neuman/gripster/references/8bitdos-official-new-xbox-mobile-controller-includes-hall-effect-sticks-and-triggers-4.large.webp

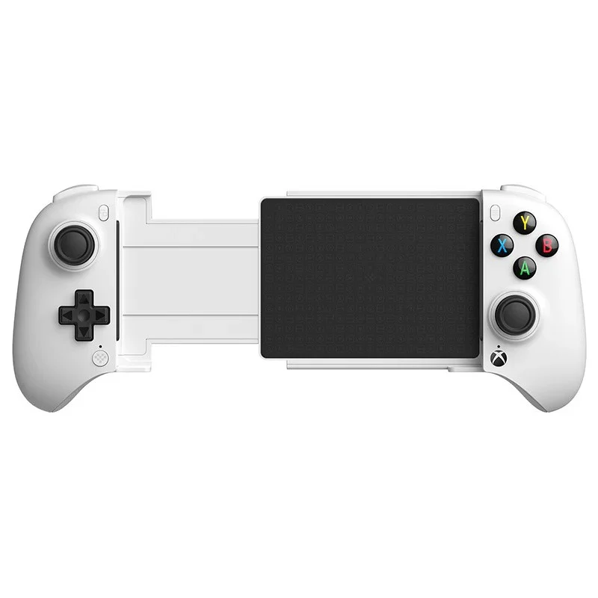
references/8bitdos-official-new-xbox-mobile-controller-includes-hall-effect-sticks-and-triggers-4.large.webp
