neuman/gripster/references/61UZpFPT2iS._AC_UF1000,1000_QL80_.jpg

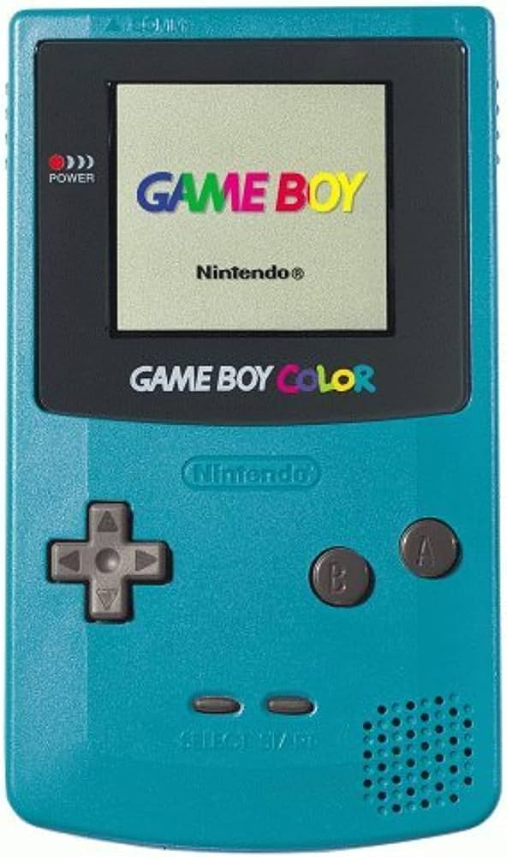
references/61UZpFPT2iS._AC_UF1000,1000_QL80_.jpg
