neuman/gripster/references/13225-tay-cam-choi-game-razer-kishi-v3-phantom-white-edition-5.jpg

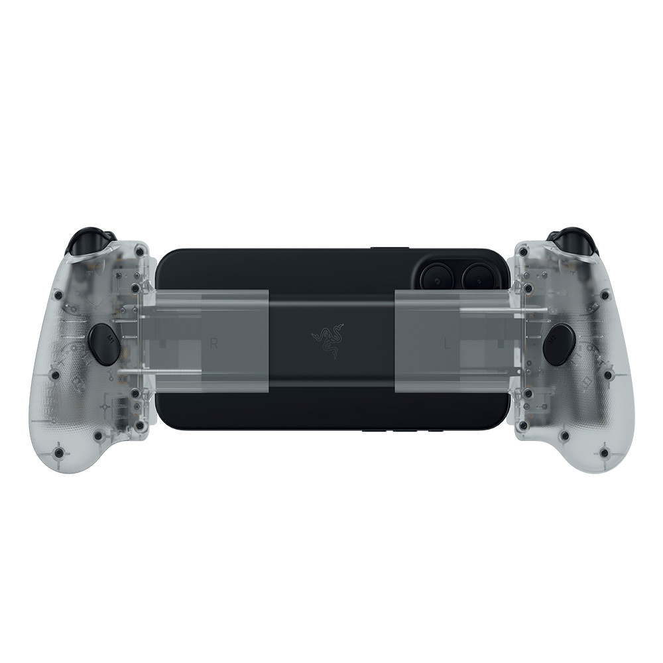
references/13225-tay-cam-choi-game-razer-kishi-v3-phantom-white-edition-5.jpg
