neuman/gripster/references/Abxylute-S9-Mobile_1.1.jpg

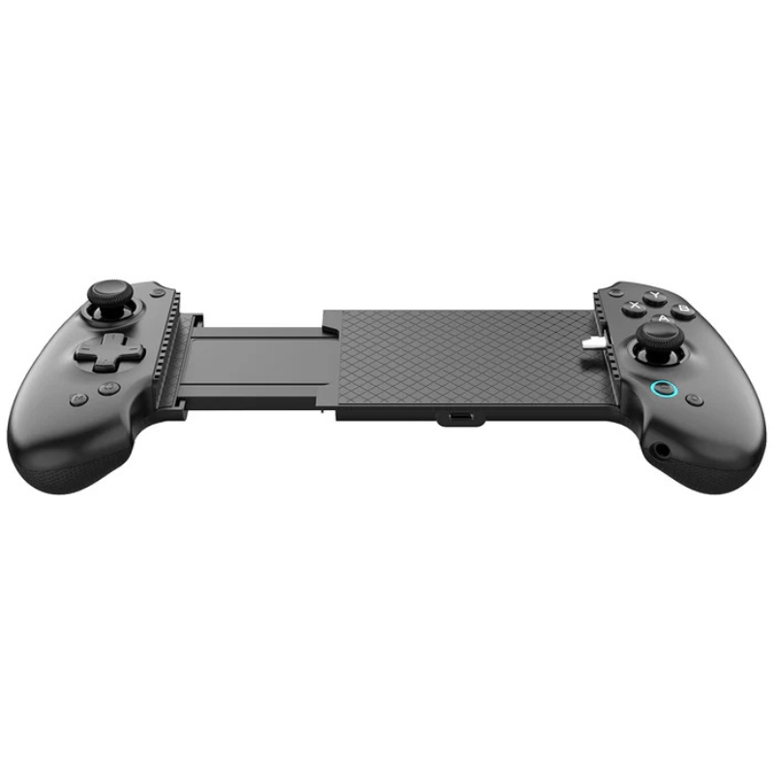
references/Abxylute-S9-Mobile_1.1.jpg
