neuman/gripster/references/backbone.jpg

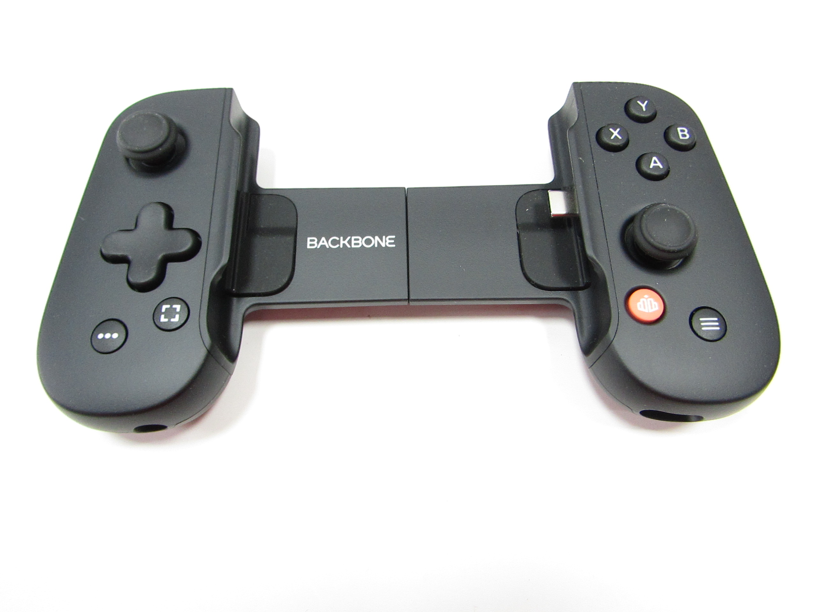
references/backbone.jpg
