neuman/gripster/references/phone_keyboard_fast_mock.jpg

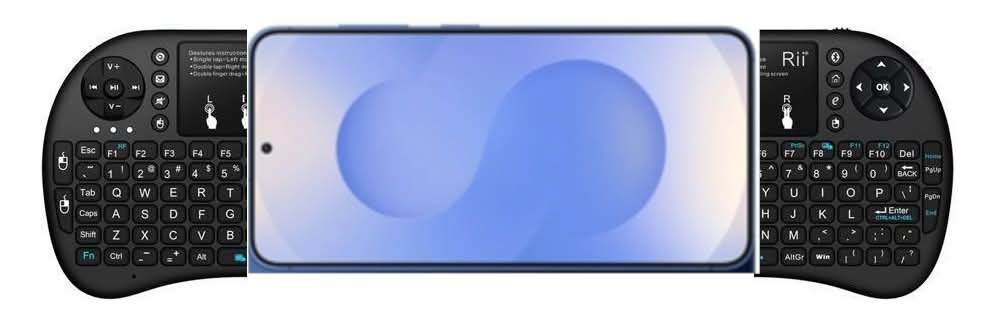
references/phone_keyboard_fast_mock.jpg
