neuman/gripster/references/razr_kishi_2.png

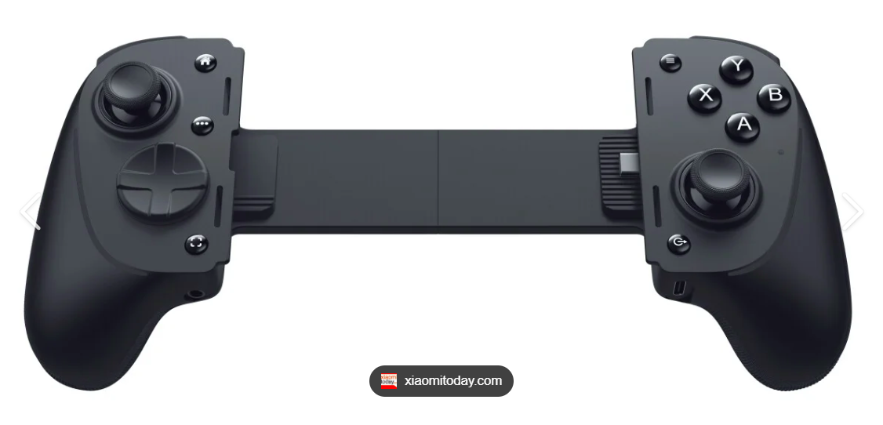
references/razr_kishi_2.png
