neuman/gripster/references/rii8_ref.png

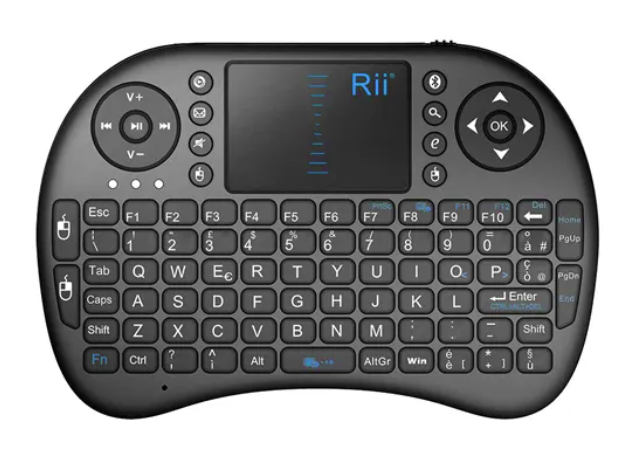
references/rii8_ref.png
