neuman/gripster/references/rii_8plus_pcb_back.png

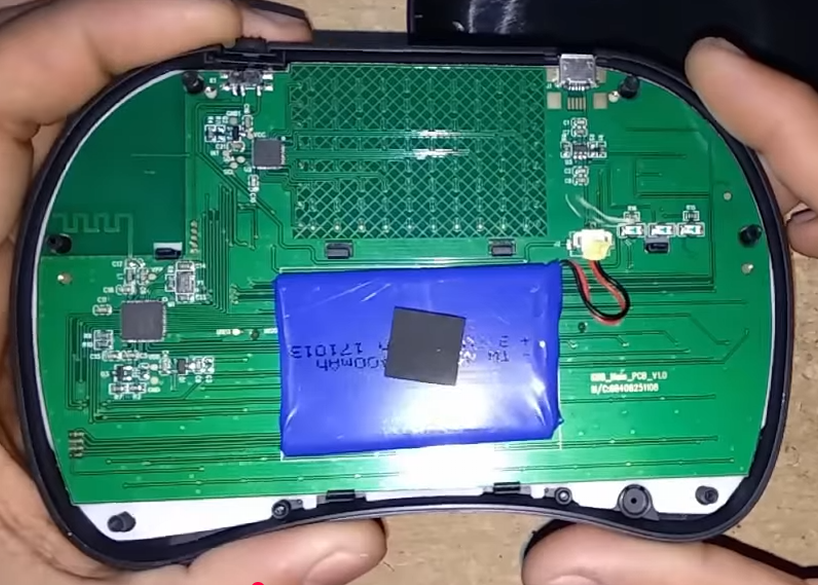
references/rii_8plus_pcb_back.png
