neuman/gripster/references/rii_8plus_pcb_front.png

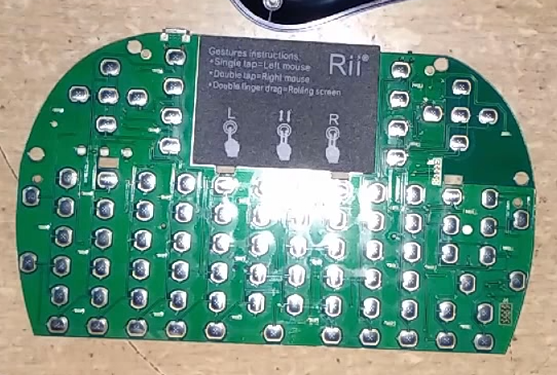
references/rii_8plus_pcb_front.png
