neuman/gripster/renders/part_back_left.png

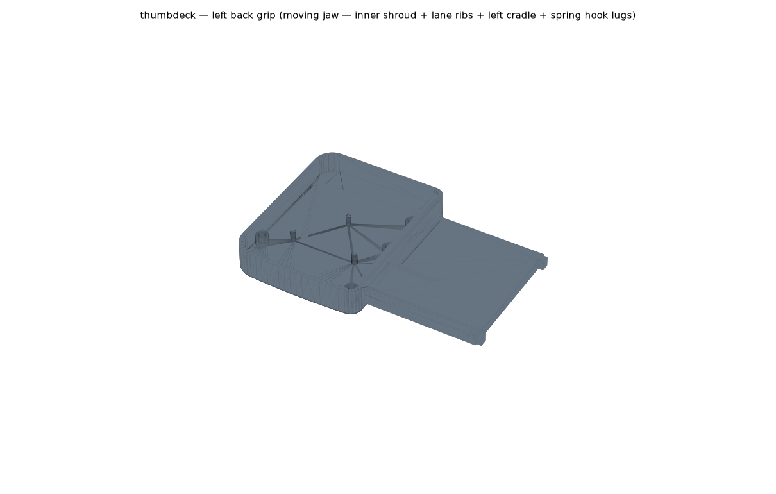
renders/part_back_left.png
