neuman/gripster/renders/part_keymat_left.png

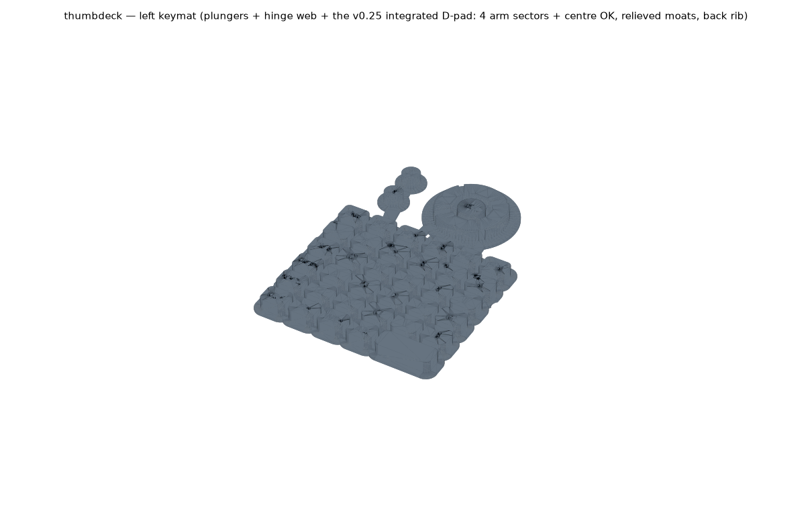
renders/part_keymat_left.png
