neuman/gripster/renders/part_nub_cap.png

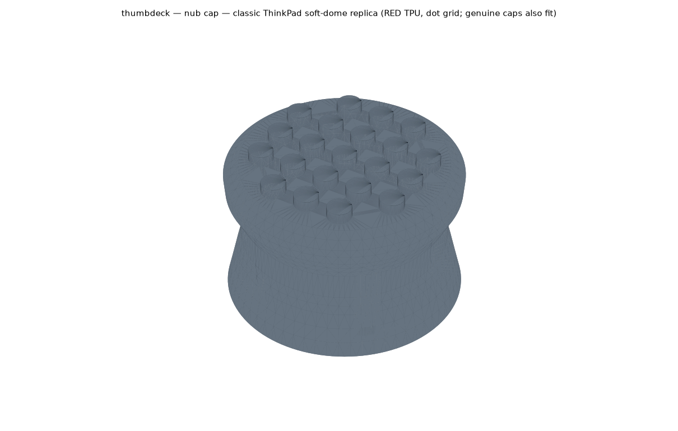
renders/part_nub_cap.png
