neuman/gripster/renders/part_nub_spring.png

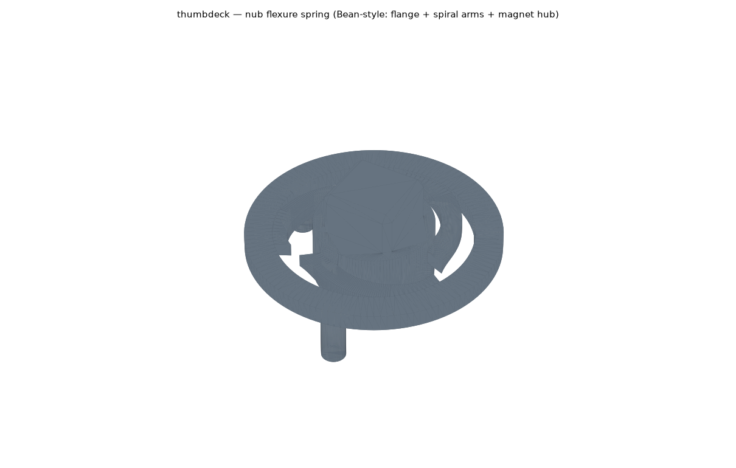
renders/part_nub_spring.png
