neuman/gripster/renders/assembly3d_exploded.png

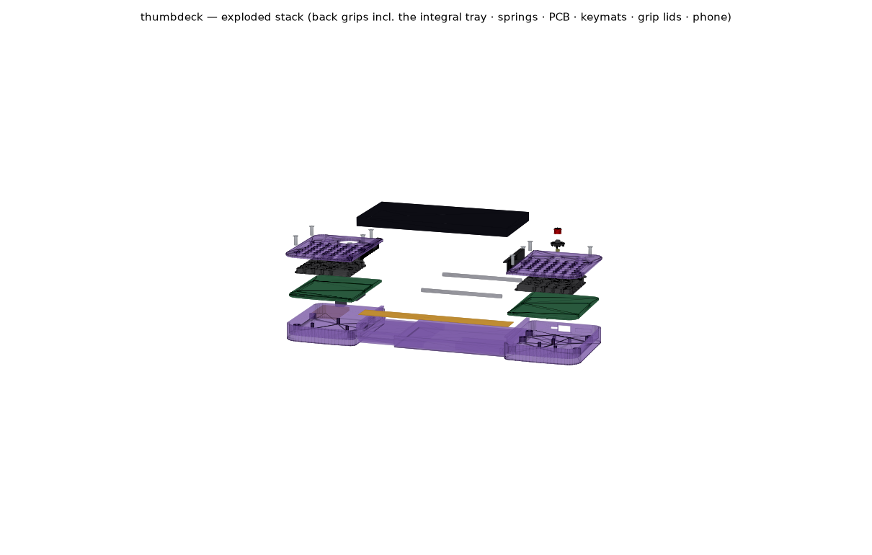
renders/assembly3d_exploded.png
