neuman/gripster/renders/history/soldermap_right_preview.png

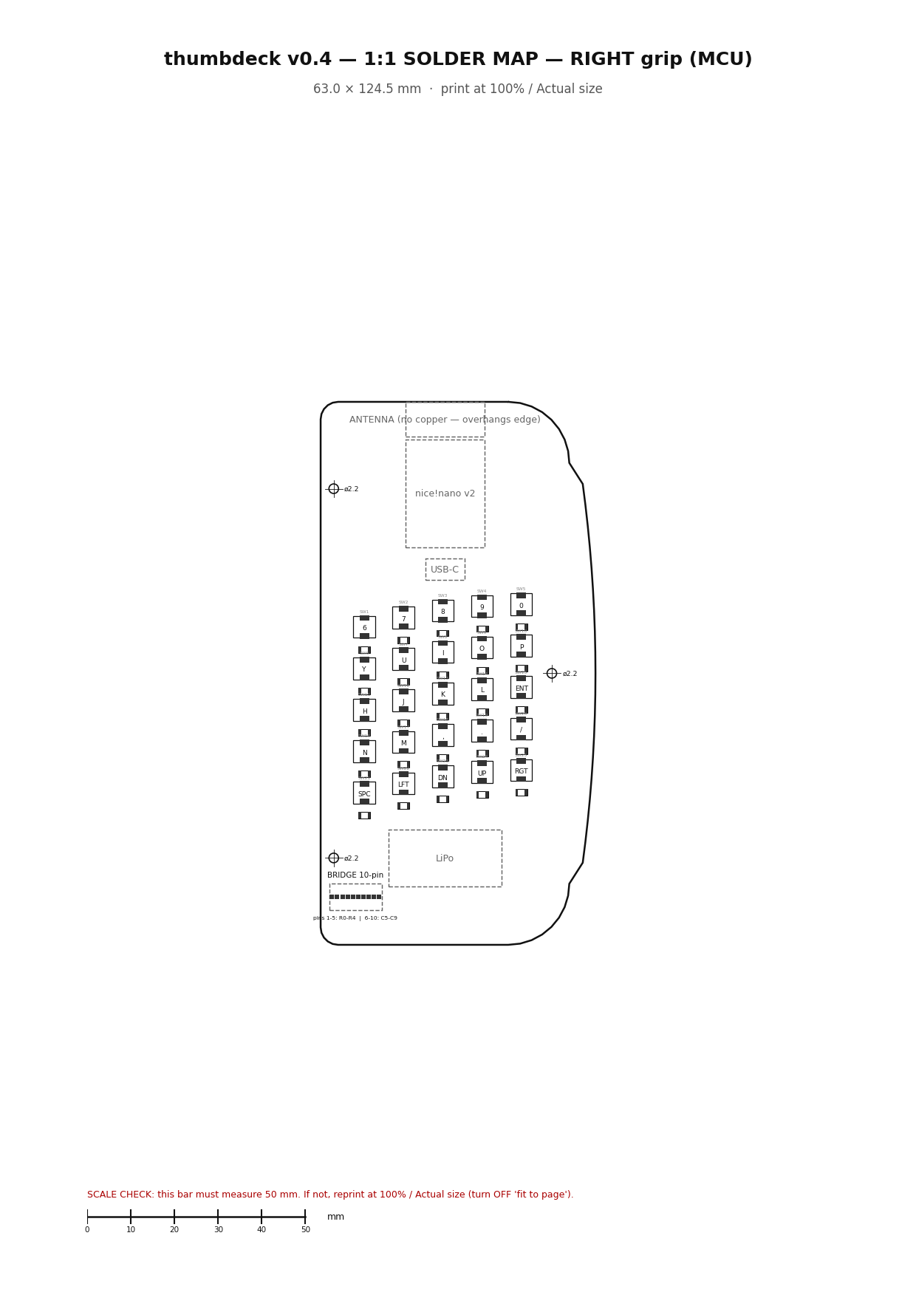
renders/history/soldermap_right_preview.png
