neuman/gripster/renders/history/iter_00.png

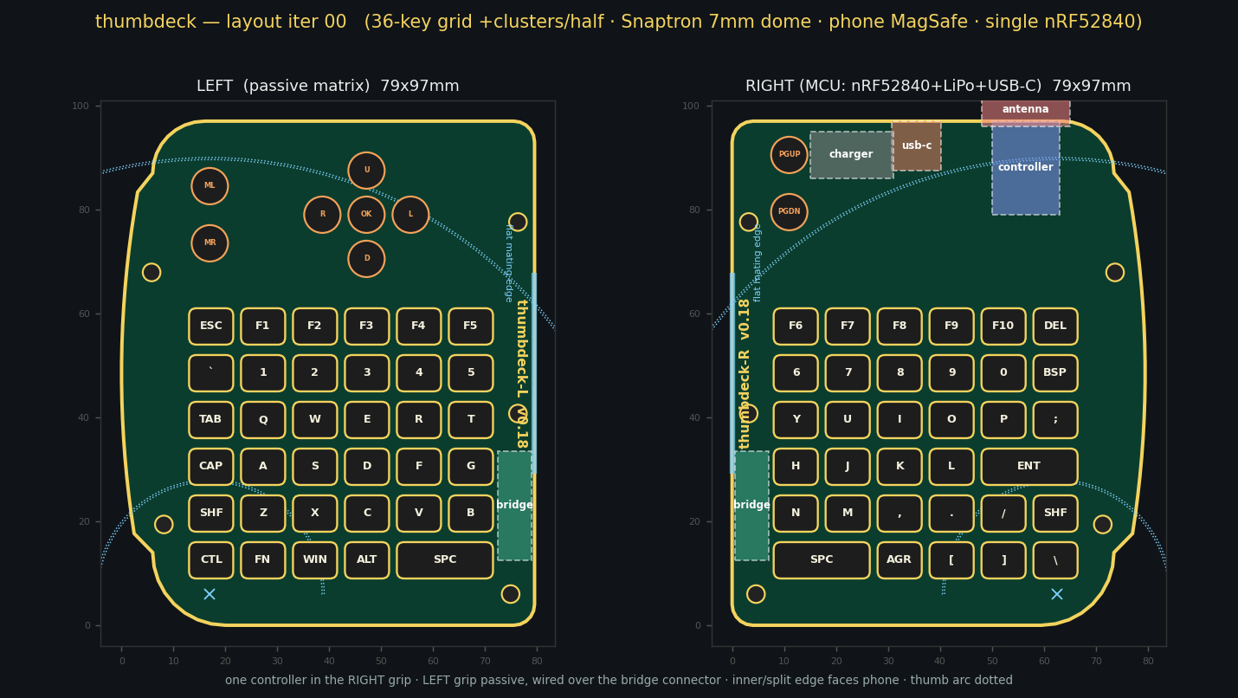
renders/history/iter_00.png
