neuman/gripster/renders/history/iter_03.png

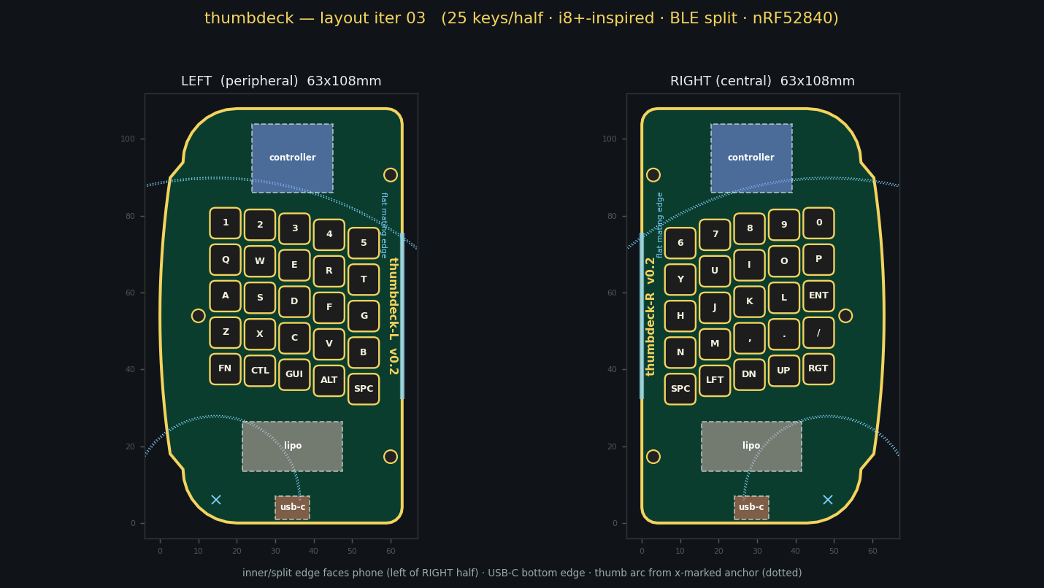
renders/history/iter_03.png
