neuman/gripster/renders/history/iter_20.png

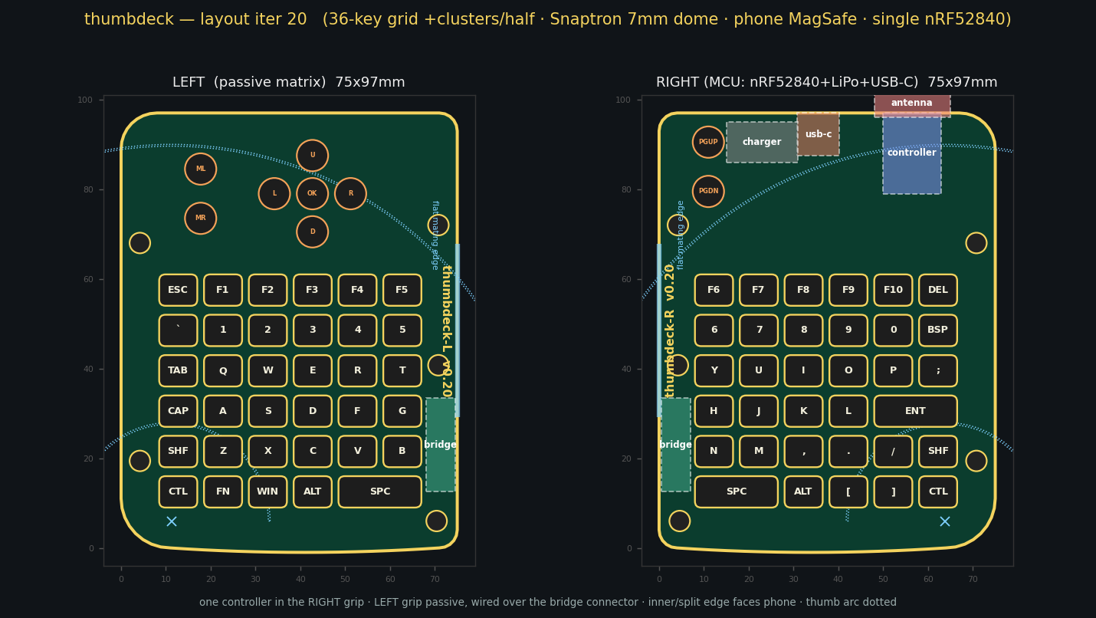
renders/history/iter_20.png
