neuman/gripster/renders/history/iter_22.png

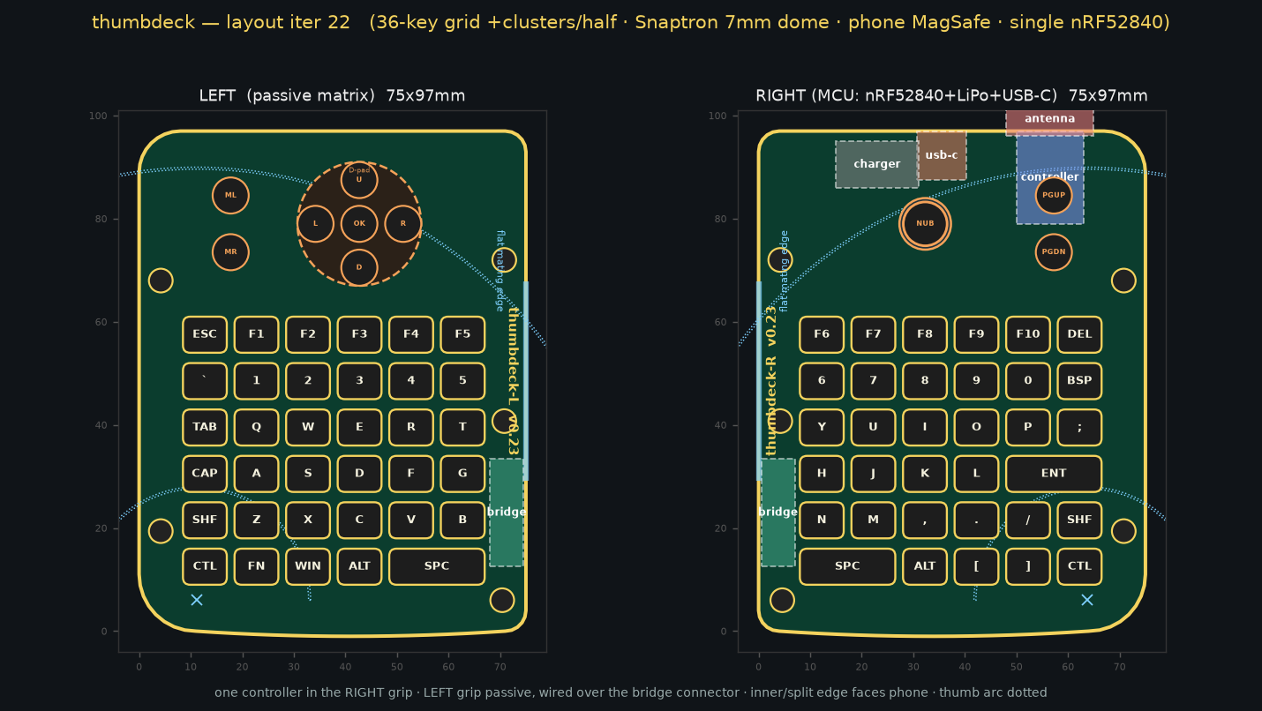
renders/history/iter_22.png
